ecurtz/RGB_DMD/recordings/SternSega/SPIKE/dmd2.png

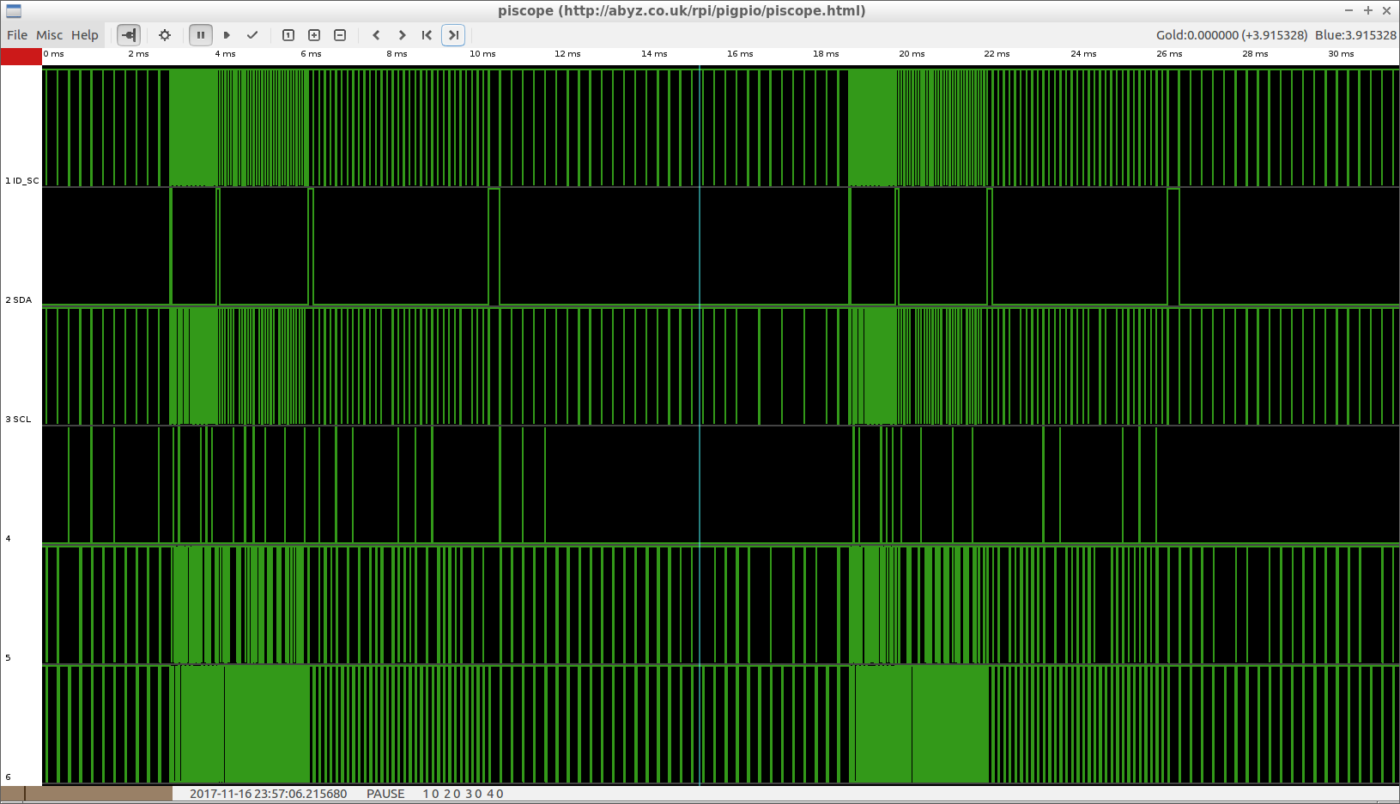
recordings/SternSega/SPIKE/dmd2.png
