ecurtz/RGB_DMD/recordings/SternSega/SPIKE/dmd2_max_zoom.png

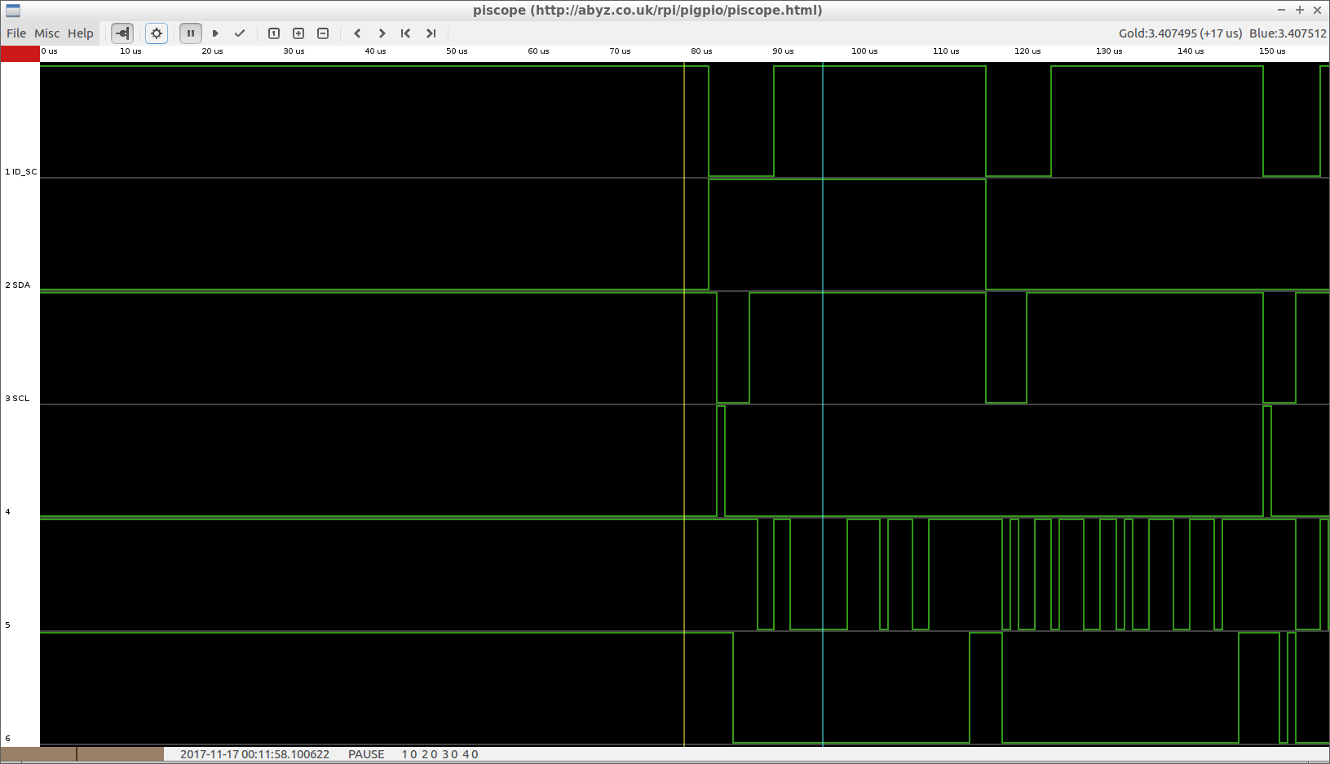
recordings/SternSega/SPIKE/dmd2_max_zoom.png
