ecurtz/RGB_DMD/recordings/SternSega/SPIKE/dmd2_zoom.png

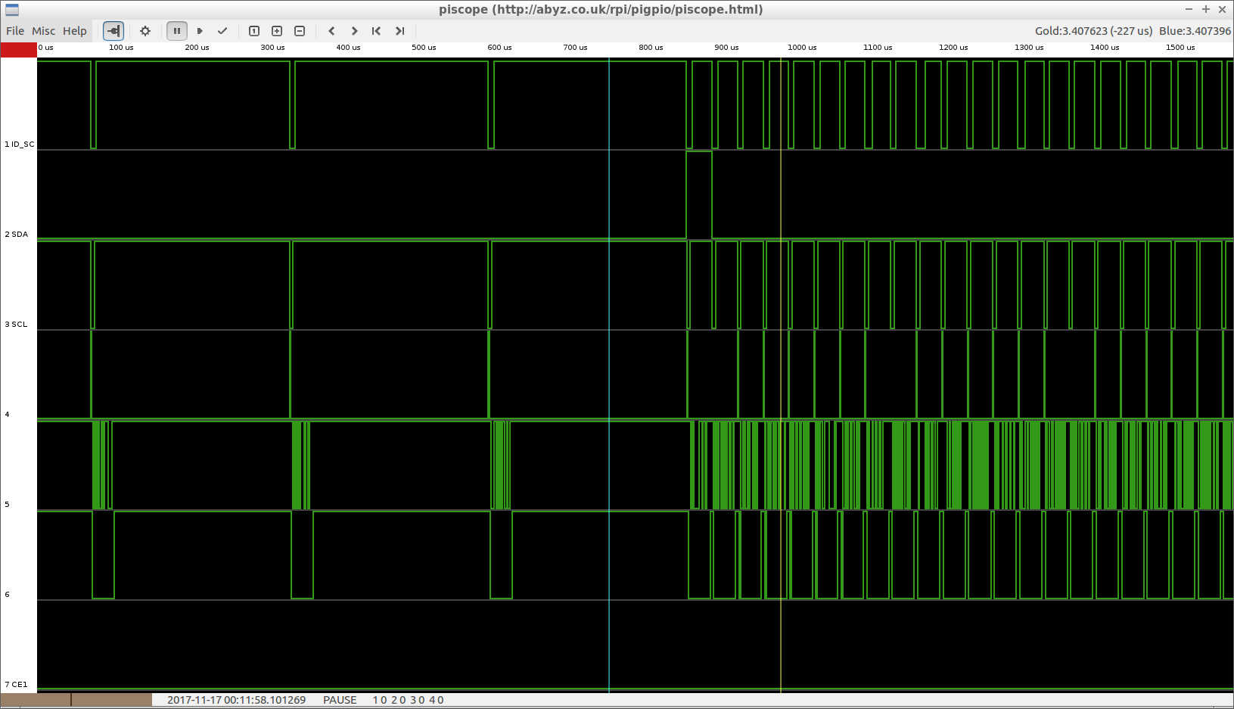
recordings/SternSega/SPIKE/dmd2_zoom.png
