ecurtz/RGB_DMD/recordings/SternSega/SPIKE/dmd3_zoom.png

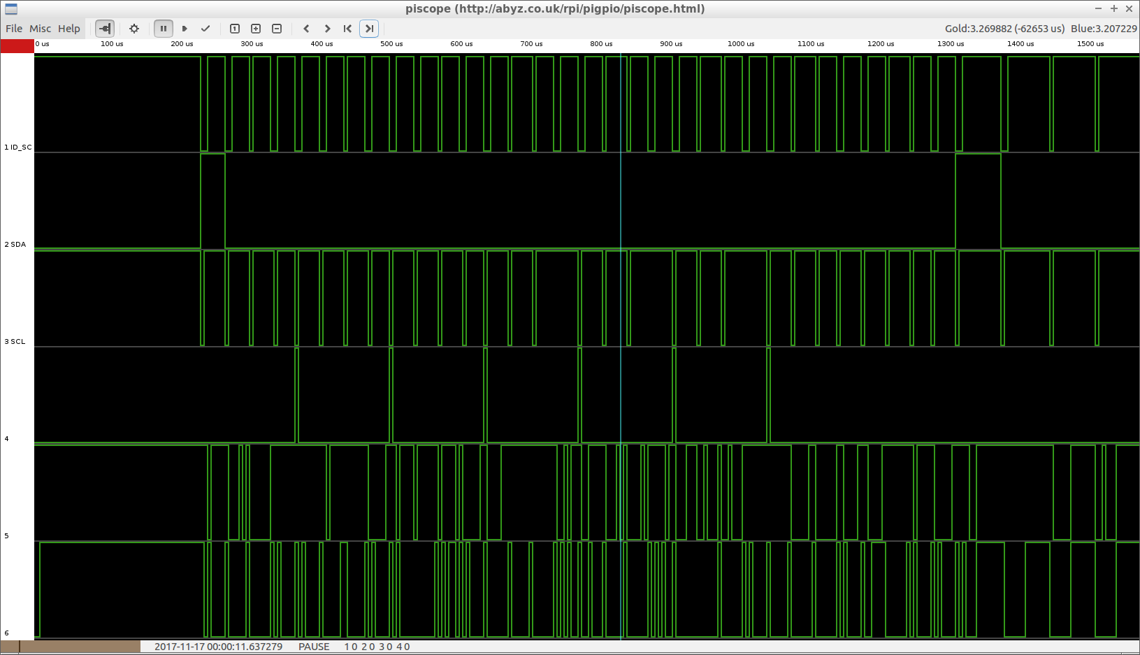
recordings/SternSega/SPIKE/dmd3_zoom.png
