ecurtz/RGB_DMD/recordings/SternSega/SPIKE/dmd.png

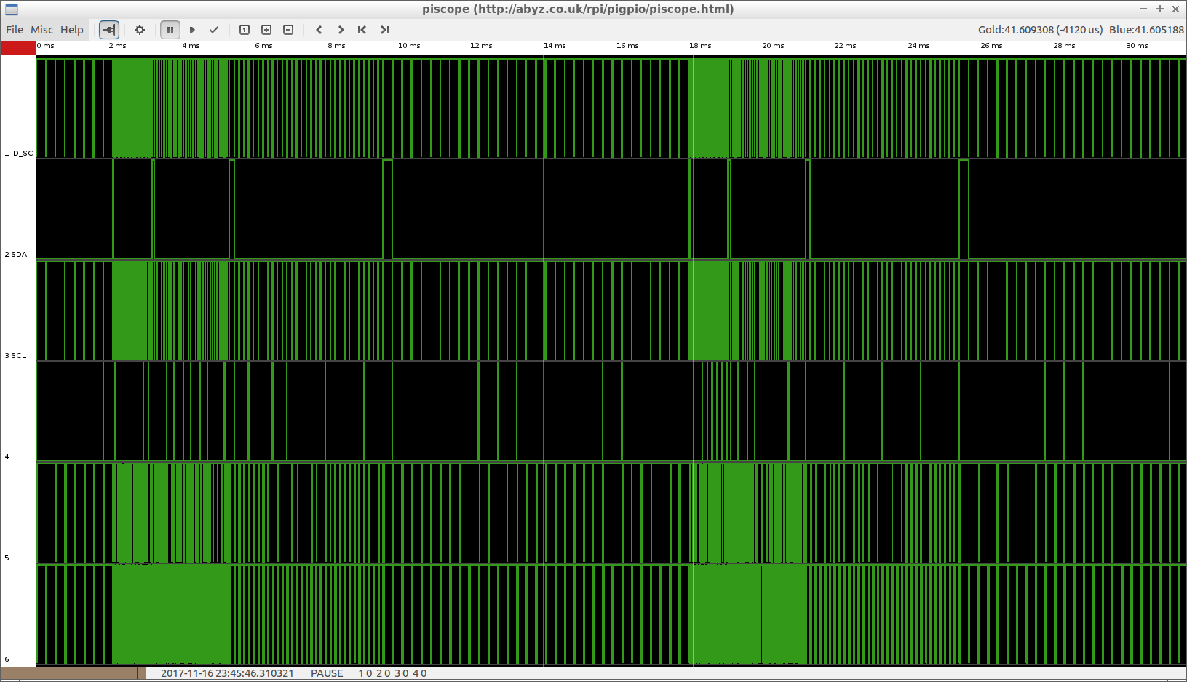
recordings/SternSega/SPIKE/dmd.png
